bazzif/semester_project/images/IMG_8064.jpg

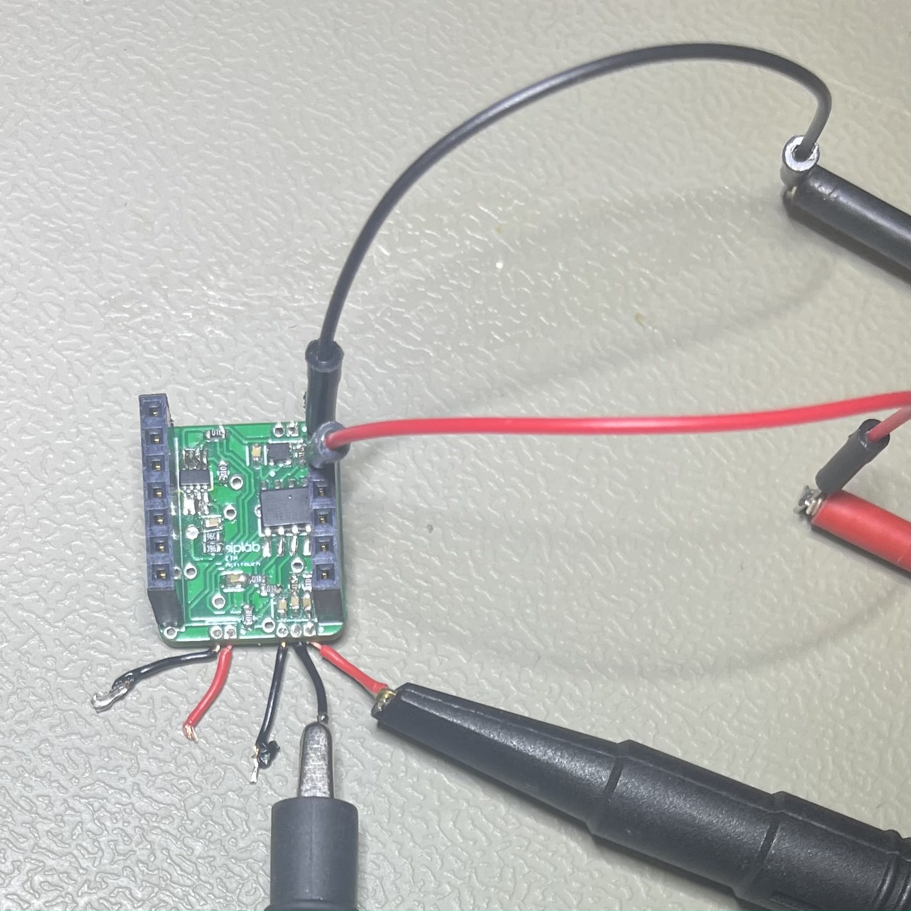
images/IMG_8064.jpg
