bazzif/semester_project/images/IMG_8065.jpg

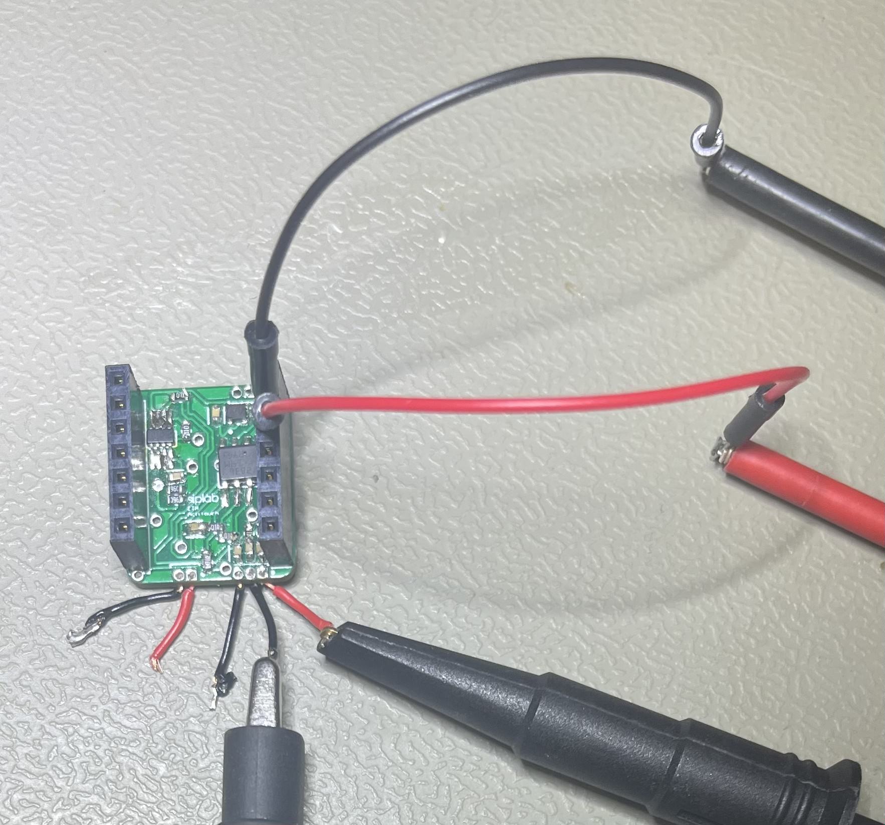
images/IMG_8065.jpg
