bazzif/semester_project/source/measurementAndEvaluation/data/SNR/SNR.xlsx

mean touch | mean no touch | sd noise
Fabio:
0.0196 | 0.0136 | 0.001 | 15.56302501
0.0196 | 0.0138 | 0.001 | 15.26855987
0.0197 | 0.0135 | 0.001 | 15.84783379
0.02 | 0.0135 | 0.001 | 16.25826713
0.02 | 0.0136 | 0.001 | 16.12359948
Ramura
0.01311 | 0.0089 | 0.00014 | 29.5630812
0.0133 | 0.008859 | 0.00014 | 30.02705475
0.013212 | 0.008778 | 0.00014 | 30.01335306
0.012729 | 0.008735 | 0.00014 | 29.1056005
0.013143 | 0.00877 | 0.00014 | 29.89302883
Philip
0.016187 | 0.009862 | 0.000221 | 29.13336512
0.015953 | 0.00988 | 0.000221 | 28.78022015
0.01552 | 0.00985 | 0.000221 | 28.1838157
0.016129 | 0.009713 | 0.000221 | 29.25744163
0.015553 | 0.009798 | 0.000221 | 28.31306109
