bazzif/semester_project/source/measurementAndEvaluation/data/pinch/DFFT.csv

=~=~=~=~=~=~=~=~=~=~=~= PuTTY log 2022.08.03 09:29:59 =~=~=~=~=~=~=~=~=~=~=~=
49108.5 | 21143.3 | 114.9 | 43.7 | 23.4 | 14.3 | 13.9 | 5.9 | 7.4 | 2.8 | 7.2 | 6.9 | 10.5 | 7.8 | 5.8 | 2.1 | 2.5 | 7.6 | 11.7 | 6.7 | 3.5 | 2.5 | 5.0 | 7.4 | 5.7 | 6.3 | 10.1 | 7.1 | 4.7 | 2.5 | 7.3 | 2.1 | 2.1 | 7.6 | 3.2 | 2.0 | 3.3 | 3.1 | 3.8 | 7.9 | 2.4 | 4.0 | 3.5 | 5.6 | 2.9 | 7.8 | 8.9 | 2.4 | 7.5 | 8.8 | 9.0 | 4.5 | 7.5 | 4.1 | 5.1 | 4.1 | 10.7 | 11.8 | 8.7 | 6.0
49095.6 | 21134.4 | 112.9 | 43.0 | 27.4 | 7.8 | 13.2 | 8.2 | 7.1 | 2.7 | 5.4 | 4.4 | 4.5 | 2.1 | 4.6 | 5.5 | 3.6 | 6.0 | 6.4 | 10.4 | 12.4 | 7.7 | 1.1 | 4.0 | 5.2 | 4.9 | 3.8 | 5.5 | 6.0 | 5.9 | 9.8 | 3.0 | 4.7 | 1.5 | 3.2 | 2.3 | 4.4 | 7.7 | 1.2 | 10.1 | 6.9 | 5.2 | 7.0 | 3.5 | 5.6 | 7.2 | 6.0 | 3.0 | 5.9 | 5.1 | 6.3 | 0.9 | 11.5 | 11.6 | 7.3 | 7.5 | 5.2 | 8.8 | 0.4 | 4.4
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
